capnajax/Tesla-Clock/service/photos/img3.jpg

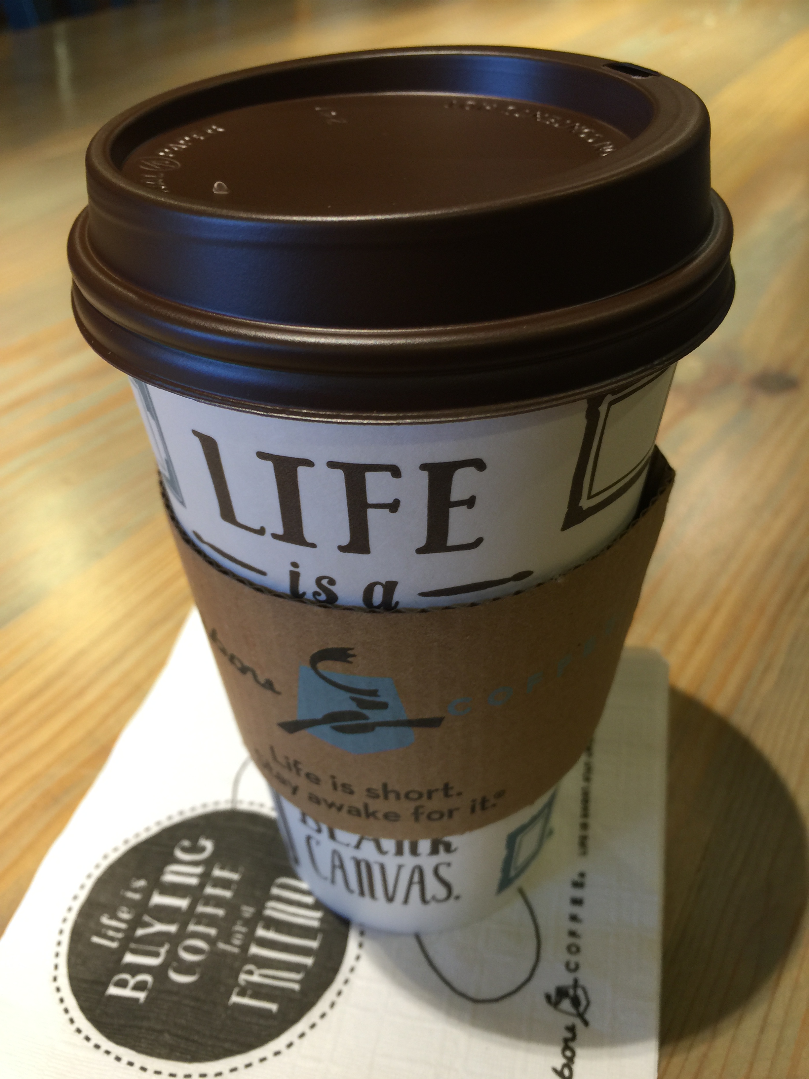
service/photos/img3.jpg
